centicosm/DiceRoller/DiceRollerConfig.h

#ifndef DICE_ROLLER_CONFIG_H
#define	DICE_ROLLER_CONFIG_H


// PIC16F88 Configuration Bit Settings


#include <xc.h>
#include <pic16f88.h>

#define _XTAL_FREQ  8000000

#define HIGH    1
#define LOW     0


// CONFIG1
#pragma config FOSC = INTOSCIO  // Oscillator Selection bits (INTRC oscillator; port I/O function on both RA6/OSC2/CLKO pin and RA7/OSC1/CLKI pin)
#pragma config WDTE = OFF       // Watchdog Timer Enable bit (WDT disabled)
#pragma config PWRTE = OFF      // Power-up Timer Enable bit (PWRT disabled)
#pragma config MCLRE = OFF      // RA5/MCLR/VPP Pin Function Select bit (RA5/MCLR/VPP pin function is digital I/O, MCLR internally tied to VDD)
#pragma config BOREN = OFF      // Brown-out Reset Enable bit (BOR disabled)
#pragma config LVP = OFF         // Low-Voltage Programming Enable bit (RB3/PGM pin has PGM function, Low-Voltage Programming enabled)
#pragma config CPD = OFF        // Data EE Memory Code Protection bit (Code protection off)
#pragma config WRT = OFF        // Flash Program Memory Write Enable bits (Write protection off)
#pragma config CCPMX = RB0      // CCP1 Pin Selection bit (CCP1 function on RB0)
#pragma config CP = OFF         // Flash Program Memory Code Protection bit (Code protection off)

// CONFIG2
#pragma config FCMEN = OFF      // Fail-Safe Clock Monitor Enable bit (Fail-Safe Clock Monitor disabled)
#pragma config IESO = OFF       // Internal External Switchover bit (Internal External Switchover mode disabled)


void Display_DiceType(void);

#endif
